colourfate/HPL/app/src/mymath.c

// the atof() function and math lib is not be surported in the SDK...

// following code come from mymath.c in F407_FC_ANO project
#include <cs_types.h>
#include <string.h>
#include <stdio.h>
#include <api_debug.h>
#include "mymath.h"

#define TAN_MAP_RES     0.003921569f     /* (smallest non-zero value in table) */
#define TAN_MAP_SIZE    256

float fast_atan_table[TAN_MAP_SIZE+1] = 
{
	0.000000e+00, 3.921549e-03, 7.842976e-03, 1.176416e-02,
	1.568499e-02, 1.960533e-02, 2.352507e-02, 2.744409e-02,
	3.136226e-02, 3.527947e-02, 3.919560e-02, 4.311053e-02,
	4.702413e-02, 5.093629e-02, 5.484690e-02, 5.875582e-02,
	6.266295e-02, 6.656816e-02, 7.047134e-02, 7.437238e-02,
	7.827114e-02, 8.216752e-02, 8.606141e-02, 8.995267e-02,
	9.384121e-02, 9.772691e-02, 1.016096e-01, 1.054893e-01,
	1.093658e-01, 1.132390e-01, 1.171087e-01, 1.209750e-01,
	1.248376e-01, 1.286965e-01, 1.325515e-01, 1.364026e-01,
	1.402496e-01, 1.440924e-01, 1.479310e-01, 1.517652e-01,
	1.555948e-01, 1.594199e-01, 1.632403e-01, 1.670559e-01,
	1.708665e-01, 1.746722e-01, 1.784728e-01, 1.822681e-01,
	1.860582e-01, 1.898428e-01, 1.936220e-01, 1.973956e-01,
	2.011634e-01, 2.049255e-01, 2.086818e-01, 2.124320e-01,
	2.161762e-01, 2.199143e-01, 2.236461e-01, 2.273716e-01,
	2.310907e-01, 2.348033e-01, 2.385093e-01, 2.422086e-01,
	2.459012e-01, 2.495869e-01, 2.532658e-01, 2.569376e-01,
	2.606024e-01, 2.642600e-01, 2.679104e-01, 2.715535e-01,
	2.751892e-01, 2.788175e-01, 2.824383e-01, 2.860514e-01,
	2.896569e-01, 2.932547e-01, 2.968447e-01, 3.004268e-01,
	3.040009e-01, 3.075671e-01, 3.111252e-01, 3.146752e-01,
	3.182170e-01, 3.217506e-01, 3.252758e-01, 3.287927e-01,
	3.323012e-01, 3.358012e-01, 3.392926e-01, 3.427755e-01,
	3.462497e-01, 3.497153e-01, 3.531721e-01, 3.566201e-01,
	3.600593e-01, 3.634896e-01, 3.669110e-01, 3.703234e-01,
	3.737268e-01, 3.771211e-01, 3.805064e-01, 3.838825e-01,
	3.872494e-01, 3.906070e-01, 3.939555e-01, 3.972946e-01,
	4.006244e-01, 4.039448e-01, 4.072558e-01, 4.105574e-01,
	4.138496e-01, 4.171322e-01, 4.204054e-01, 4.236689e-01,
	4.269229e-01, 4.301673e-01, 4.334021e-01, 4.366272e-01,
	4.398426e-01, 4.430483e-01, 4.462443e-01, 4.494306e-01,
	4.526070e-01, 4.557738e-01, 4.589307e-01, 4.620778e-01,
	4.652150e-01, 4.683424e-01, 4.714600e-01, 4.745676e-01,
	4.776654e-01, 4.807532e-01, 4.838312e-01, 4.868992e-01,
	4.899573e-01, 4.930055e-01, 4.960437e-01, 4.990719e-01,
	5.020902e-01, 5.050985e-01, 5.080968e-01, 5.110852e-01,
	5.140636e-01, 5.170320e-01, 5.199904e-01, 5.229388e-01,
	5.258772e-01, 5.288056e-01, 5.317241e-01, 5.346325e-01,
	5.375310e-01, 5.404195e-01, 5.432980e-01, 5.461666e-01,
	5.490251e-01, 5.518738e-01, 5.547124e-01, 5.575411e-01,
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
};


static double mx_sin(double rad)
{   
	double sine;
	/* Same strip exception */
	if ((float)rad < 0)
		sine = rad*(1.27323954f + 0.405284735f * rad);
	else
		sine = rad * (1.27323954f - 0.405284735f * rad);
	if ((float)sine < 0)
		sine = sine*(-0.225f * (sine + 1) + 1);
	else
		sine = sine * (0.225f *( sine - 1) + 1);
		
	return sine;
}

double my_sin(double rad)
{
	s8 flag = 1;

	if ((float)rad >= ONE_PI)
	{
		rad -= ONE_PI;
		flag = -1;
	}
	
	return mx_sin(rad) * flag;
}

double my_cos(double rad)
{
	s8 flag = 1;
	rad += ONE_PI/2.0;

	if ((float)rad >= ONE_PI)
	{
		flag = -1;
		rad -= ONE_PI;
	}


	return my_sin(rad)*flag;
}

float my_sqrt(float number)
{
	long i;
	float x, y;
	const float f = 1.5F;
	x = number * 0.5F;
	y = number;
	i = * ( long * ) &y;
	i = 0x5f3759df - ( i >> 1 );

	y = * ( float * ) &i;
	y = y * ( f - ( x * y * y ) );
	y = y * ( f - ( x * y * y ) );
	return number * y;
}

REAL fast_atan2(REAL y, REAL x) 
{
	REAL x_abs, y_abs, z;
	REAL alpha, angle, base_angle;
	int index;

	/* don't divide by zero! */
	if ((y == 0.0f) || (x == 0.0f))//if ((y == 0.0f) && (x == 0.0f))
		angle = 0.0f;
	else 
	{
		/* normalize to +/- 45 degree range */
		y_abs = my_abs(y);
		x_abs = my_abs(x);
		//z = (y_abs < x_abs ? y_abs / x_abs : x_abs / y_abs);
		if (y_abs < x_abs)
			z = y_abs / x_abs;
		else
			z = x_abs / y_abs;
		/* when ratio approaches the table resolution, the angle is */
		/*      best approximated with the argument itself...       */
		if (z < TAN_MAP_RES)
			base_angle = z;
		else 
		{
			/* find index and interpolation value */
			alpha = z * (REAL) TAN_MAP_SIZE - .5f;
			index = (int) alpha;
			alpha -= (REAL) index;
			/* determine base angle based on quadrant and */
			/* add or subtract table value from base angle based on quadrant */
			base_angle = fast_atan_table[index];
			base_angle += (fast_atan_table[index + 1] - fast_atan_table[index]) * alpha;
		}

		if (x_abs > y_abs) 
		{        /* -45 -> 45 or 135 -> 225 */
			if (x >= 0.0f) 
			{           /* -45 -> 45 */
				if (y >= 0.0f)
					angle = base_angle;   /* 0 -> 45, angle OK */
				else
					angle = -base_angle;  /* -45 -> 0, angle = -angle */
			} 
			else
			{                  /* 135 -> 180 or 180 -> -135 */
				angle = 3.14159265358979323846;

				if (y >= 0.0f)
					angle -= base_angle;  /* 135 -> 180, angle = 180 - angle */
				else
					angle = base_angle - angle;   /* 180 -> -135, angle = angle - 180 */
			}
		} 
		else 
		{                    /* 45 -> 135 or -135 -> -45 */
			if (y >= 0.0f) 
			{           /* 45 -> 135 */
				angle = 1.57079632679489661923;

				if (x >= 0.0f)
					angle -= base_angle;  /* 45 -> 90, angle = 90 - angle */
				else
					angle += base_angle;  /* 90 -> 135, angle = 90 + angle */
			} 
			else
			{                  /* -135 -> -45 */
				angle = -1.57079632679489661923;

				if (x >= 0.0f)
					angle += base_angle;  /* -90 -> -45, angle = -90 + angle */
				else
					angle -= base_angle;  /* -135 -> -90, angle = -90 - angle */
			}
		}
	}

#ifdef ZERO_TO_TWOPI
	if (angle < 0)
		return (angle + TWOPI);
	else
		return (angle);
#else
	return (angle);
#endif
}


int isfinite(float v)
{
	return 1;
}

float my_atof(char *str)
{
	double s=0.0;
	double d=10.0;
	
	if(!(*str>='0' && *str<='9'))
        return s;  
  
    while(*str>='0'&&*str<='9'&&*str!='.') 
    {  
        s=s*10.0+*str-'0';  
        str++;  
    }  
  
    if(*str=='.')
        str++;  
  
    while(*str>='0'&&*str<='9')
    {  
        s=s+(*str-'0')/d;  
        d*=10.0;  
        str++;  
    }
	return s;
}


char *my_ftoa(double x)
{
	static char str_buf[20];
	int i, c = 0;
	memset(str_buf, 0, sizeof(str_buf));
	while(x > 1){
		x /= 10;
		c++;
	}
	for(i=0; i<16; i++){
		if(i == c){
			str_buf[i] = '.';
			continue;
		}
		x *= 10;
		str_buf[i] = (int)x + '0';
		x -= (int)x;
	}
	return str_buf;
}
